jeroenhn/zykl/KiCAD Project/Additional Libraries/3D Models/MC33270 Heatsink.stp

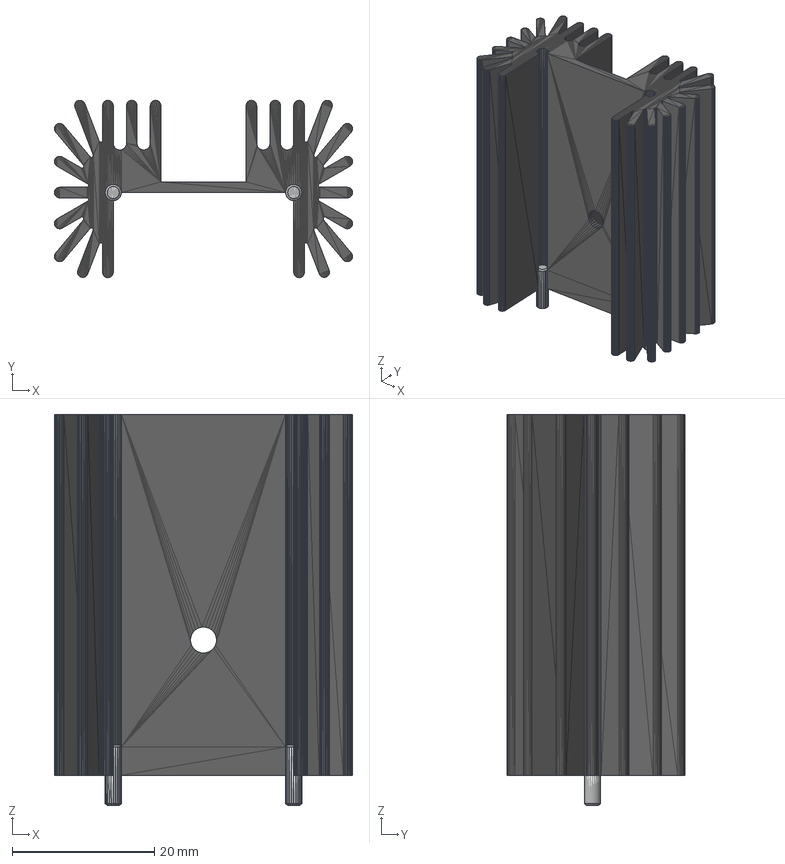
[picture p16: CAD file, 2025-12-29]
KiCAD Project/Additional Libraries/3D Models/MC33270 Heatsink.stp
42.0 x 25.0 x 55.0 mm
