jeroenhn/zykl/KiCAD Project/Additional Libraries/Molex KK 396 3D Models/026192051.stp

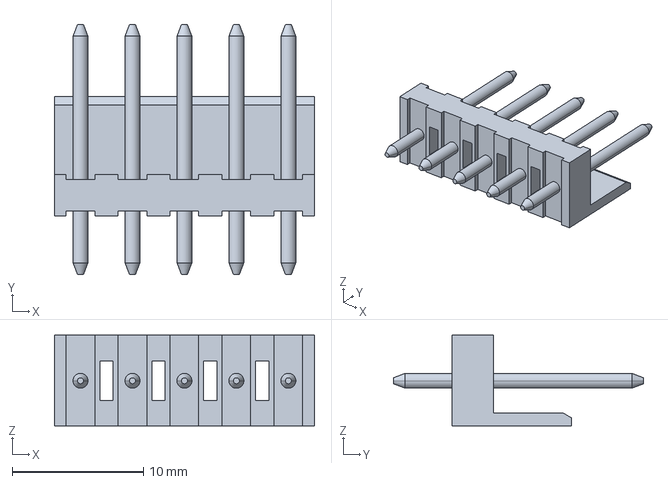
[picture p17: CAD file, 2025-12-29]
KiCAD Project/Additional Libraries/Molex KK 396 3D Models/026192051.stp
19.8 x 19.1 x 6.90 mm
